mpeccable/Vroomba/Code/test_get_address.ino

#include <Bluepad32.h>
GamepadPtr myGamepads[BP32_MAX_GAMEPADS];


// This callback gets called any time a new gamepad is connected, up to 4 at the same time.
void onConnectedGamepad(GamepadPtr gp) {
    for (int i = 0; i < BP32_MAX_GAMEPADS; i++) {
        if (myGamepads[i] == nullptr) {
            Serial.printf("CALLBACK: Gamepad is connected, index=%d\n", i);

//            GamepadProperties properties = gp->getProperties();
//            Serial.printf("Gamepad model: %s, VID=0x%04x, PID=0x%04x\n", gp->getModelName().c_str(), properties.vendor_id, properties.product_id);
//            myGamepads[i] = gp;

            const uint8_t* addr = BP32.localBdAddress();
            Serial.printf("BD Addr: %2X:%2X:%2X:%2X:%2X:%2X\n", addr[0], addr[1], addr[2], addr[3], addr[4], addr[5]);
            
            break;
        }
    }
}

void onDisconnectedGamepad(GamepadPtr gp) {
    for (int i = 0; i < BP32_MAX_GAMEPADS; i++) {
        if (myGamepads[i] == gp) {
            Serial.printf("CALLBACK: Gamepad is disconnected from index=%d\n", i);
            myGamepads[i] = nullptr;
            break;
        }
    }
}

void setup() {
    Serial.begin(115200);
    Serial.printf("Firmware: %s\n", BP32.firmwareVersion());
    const uint8_t* addr = BP32.localBdAddress();
    Serial.printf("BD Addr: %2X:%2X:%2X:%2X:%2X:%2X\n", addr[0], addr[1], addr[2], addr[3], addr[4], addr[5]);

    BP32.setup(&onConnectedGamepad, &onDisconnectedGamepad);
    BP32.forgetBluetoothKeys();
}


void loop() {
    BP32.update();
    for (int i = 0; i < BP32_MAX_GAMEPADS; i++) {
        GamepadPtr myGamepad = myGamepads[i];
        }
    delay(10);
}
